TSP-hork/R.I.G.E.L_Robotic_Manipulator/cad/manufacturing/stl/RIGEL/Reducers/20to1/final_20_1_fastdisk_1.1.stl

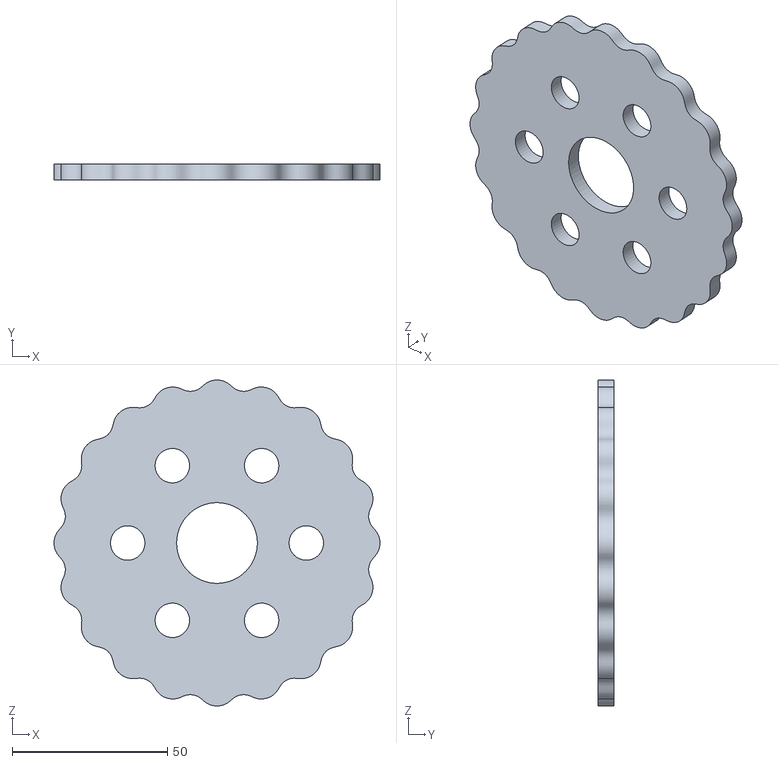
[picture p15: CAD file, 2026-10-07]
cad/manufacturing/stl/RIGEL/Reducers/20to1/final_20_1_fastdisk_1.1.stl
105.0 x 5.00 x 105.0
