TSP-hork/R.I.G.E.L_Robotic_Manipulator/cad/manufacturing/stl/RIGEL/Reducers/Adapter/adapter_V1.stl

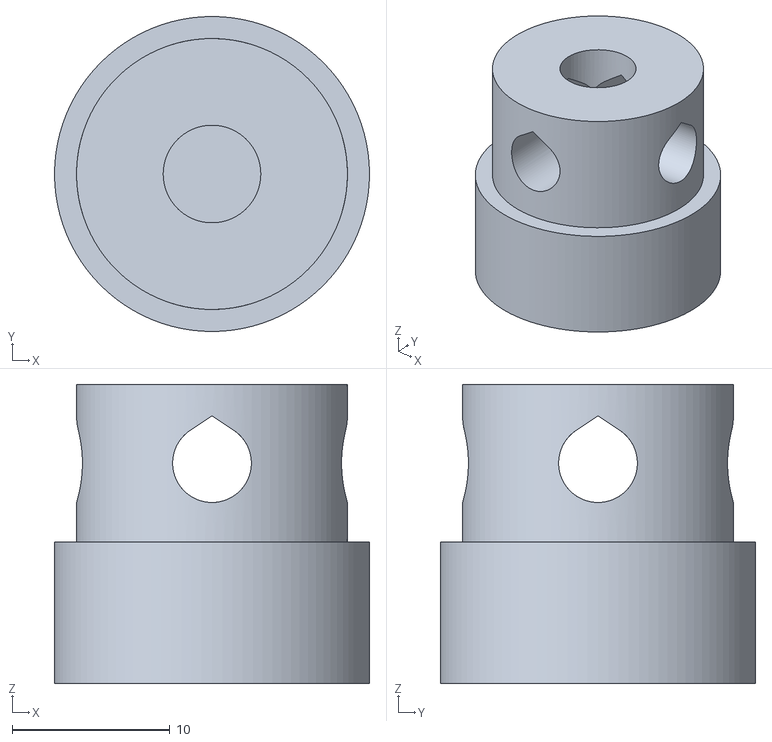
[picture p16: CAD file, 2026-10-07]
cad/manufacturing/stl/RIGEL/Reducers/Adapter/adapter_V1.stl
20.0 x 20.0 x 19.0
