TSP-hork/R.I.G.E.L_Robotic_Manipulator/cad/manufacturing/stl/RIGEL/Shoulder_Clevis_Mount/wheel_60.stl

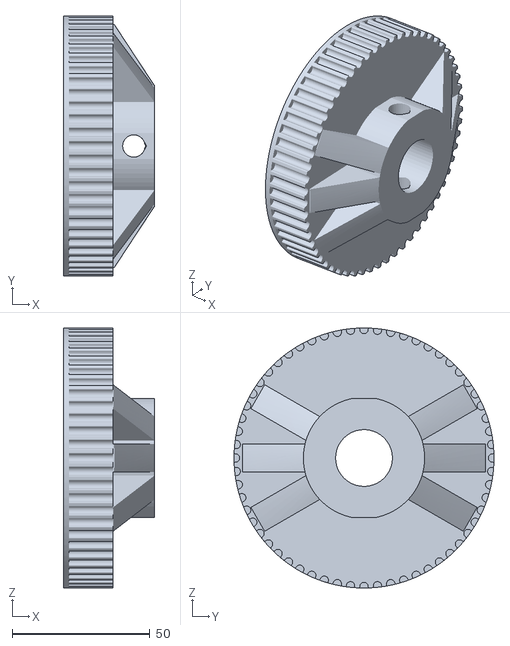
[picture p17: CAD file, 2026-10-07]
cad/manufacturing/stl/RIGEL/Shoulder_Clevis_Mount/wheel_60.stl
33.0 x 94.3 x 94.3
