TSP-hork/R.I.G.E.L_Robotic_Manipulator/cad/manufacturing/stl/RIGEL/Shoulder_module_short/Left_ear.stl

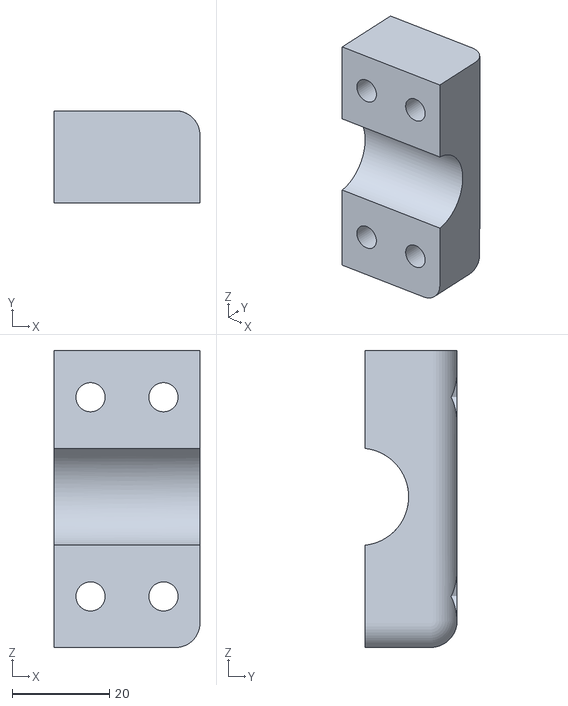
[picture p18: CAD file, 2026-10-07]
cad/manufacturing/stl/RIGEL/Shoulder_module_short/Left_ear.stl
30.0 x 19.0 x 61.1
