TSP-hork/R.I.G.E.L_Robotic_Manipulator/cad/manufacturing/stl/RIGEL/Actuator_module/Actuator_module_part.stl

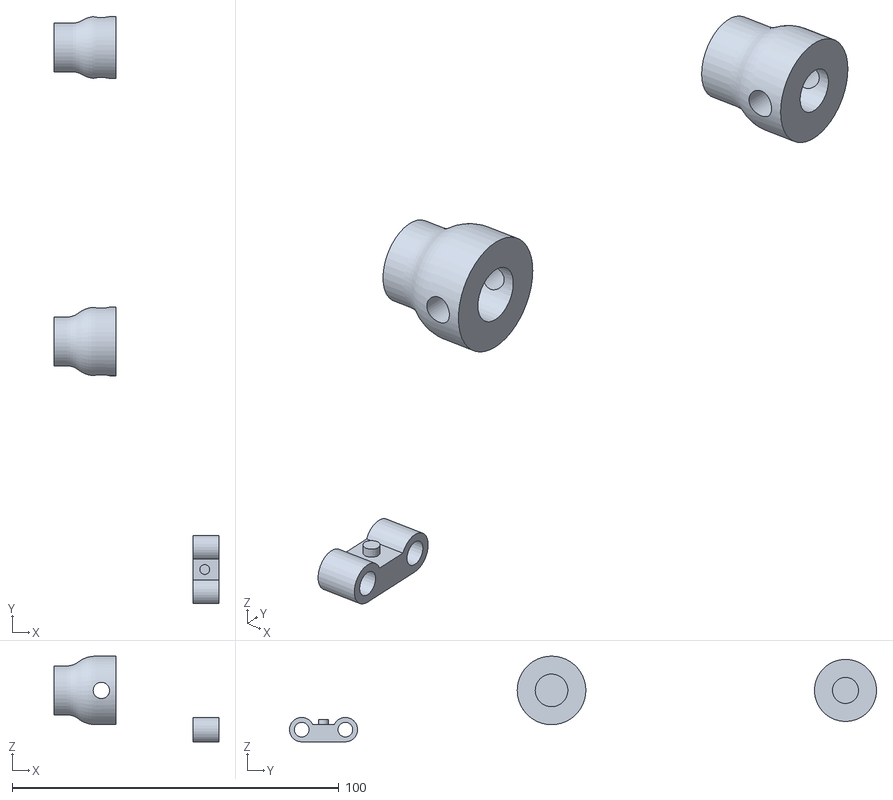
[picture p19: CAD file, 2026-10-07]
cad/manufacturing/stl/RIGEL/Actuator_module/Actuator_module_part.stl
50.5 x 179.7 x 26.3
