TSP-hork/R.I.G.E.L_Robotic_Manipulator/cad/manufacturing/stl/RIGEL/Reducers/Adapter/adapter_rotary_reducer_V1.1.stl

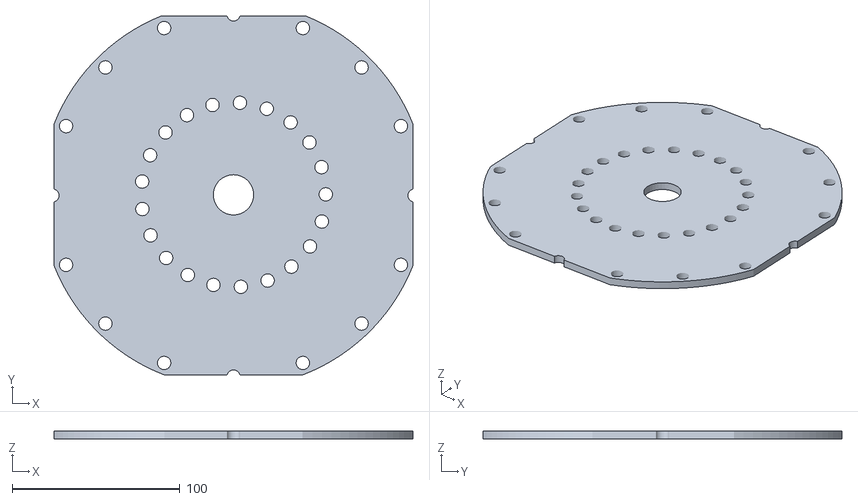
[picture p20: CAD file, 2026-10-07]
cad/manufacturing/stl/RIGEL/Reducers/Adapter/adapter_rotary_reducer_V1.1.stl
214.0 x 214.0 x 5.00
