TSP-hork/R.I.G.E.L_Robotic_Manipulator/cad/manufacturing/stl/RIGEL/Shoulder_Clevis_Mount/Shoulder_Clevis_Mount_V1.3_part.stl

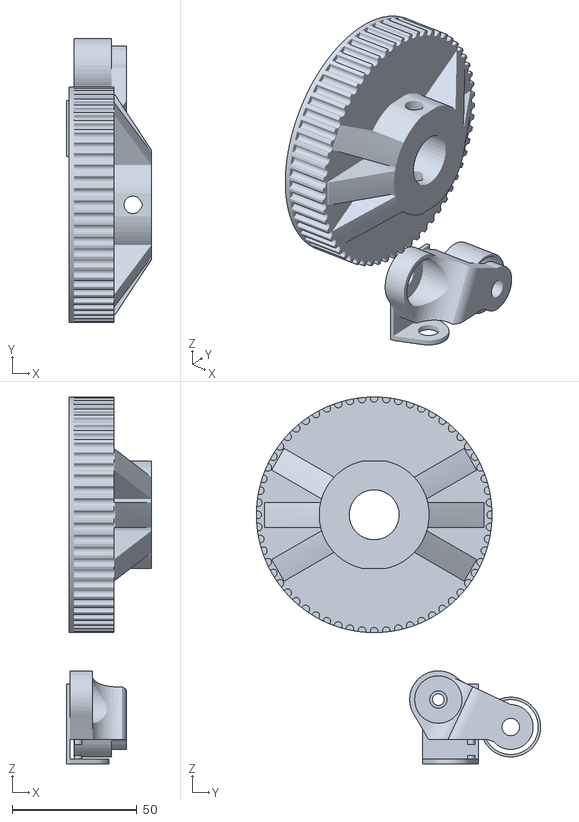
[picture p21: CAD file, 2026-10-07]
cad/manufacturing/stl/RIGEL/Shoulder_Clevis_Mount/Shoulder_Clevis_Mount_V1.3_part.stl
34.0 x 113.8 x 147.0
