TSP-hork/R.I.G.E.L_Robotic_Manipulator/cad/manufacturing/stl/RIGEL/Shoulder_module_long/Body_of_1shoulder_module_V1.2_down.stl

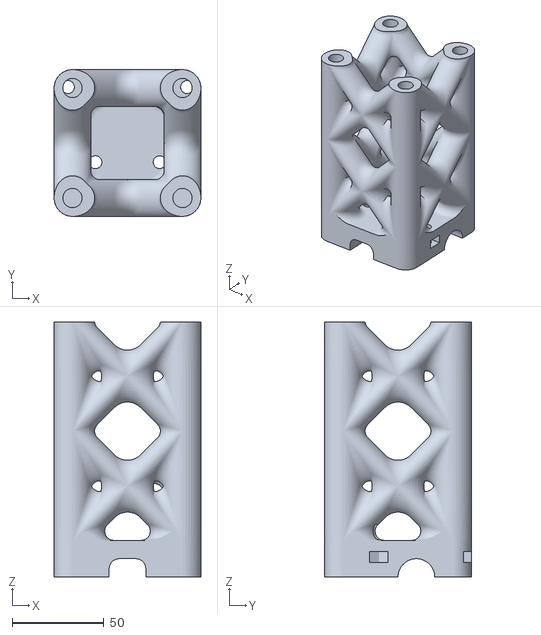
[picture p22: CAD file, 2026-10-07]
cad/manufacturing/stl/RIGEL/Shoulder_module_long/Body_of_1shoulder_module_V1.2_down.stl
80.0 x 80.0 x 139.0
