TSP-hork/R.I.G.E.L_Robotic_Manipulator/cad/manufacturing/stl/RIGEL/Shoulder_module_short/Body_of_2shoulder_module.stl

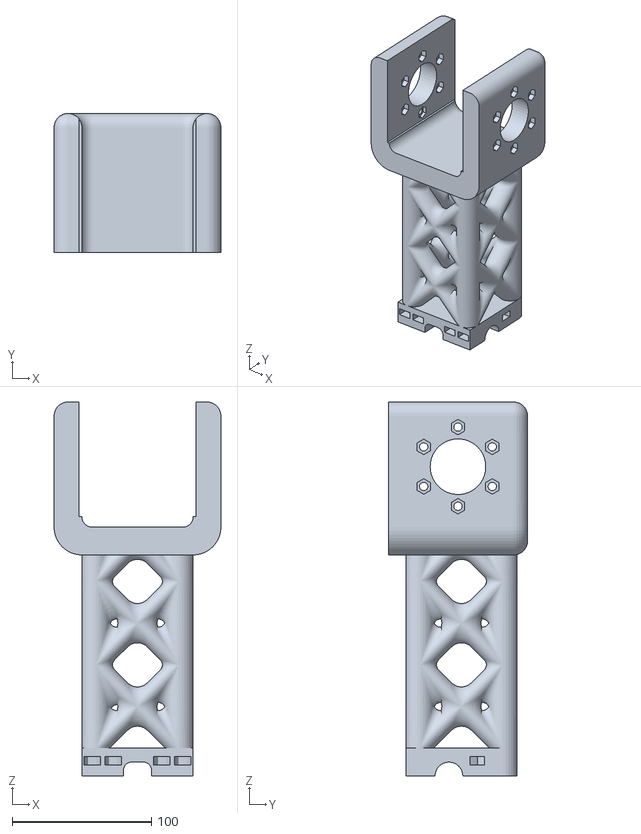
[picture p23: CAD file, 2026-10-07]
cad/manufacturing/stl/RIGEL/Shoulder_module_short/Body_of_2shoulder_module.stl
120.0 x 100.0 x 269.0
