TSP-hork/R.I.G.E.L_Robotic_Manipulator/cad/manufacturing/stl/RIGEL/Reducers/Adapter/adapter_V1.1_8mm.stl

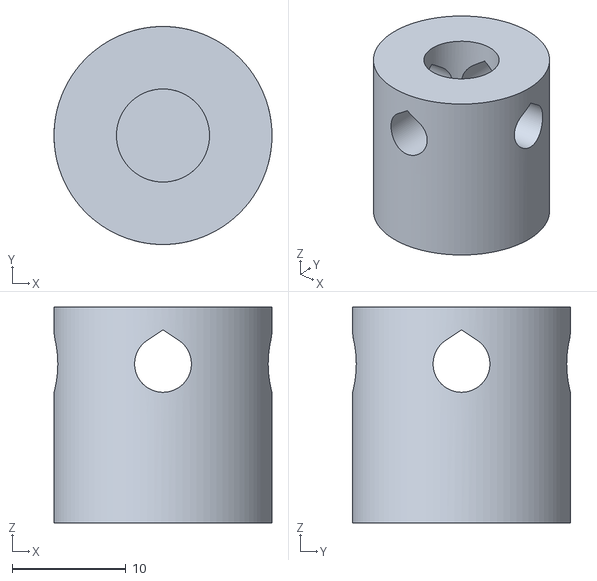
[picture p24: CAD file, 2026-10-07]
cad/manufacturing/stl/RIGEL/Reducers/Adapter/adapter_V1.1_8mm.stl
19.2 x 19.2 x 19.0
