TSP-hork/R.I.G.E.L_Robotic_Manipulator/cad/manufacturing/stl/RIGEL/Shoulder_Clevis_Mount/stator_holder.stl

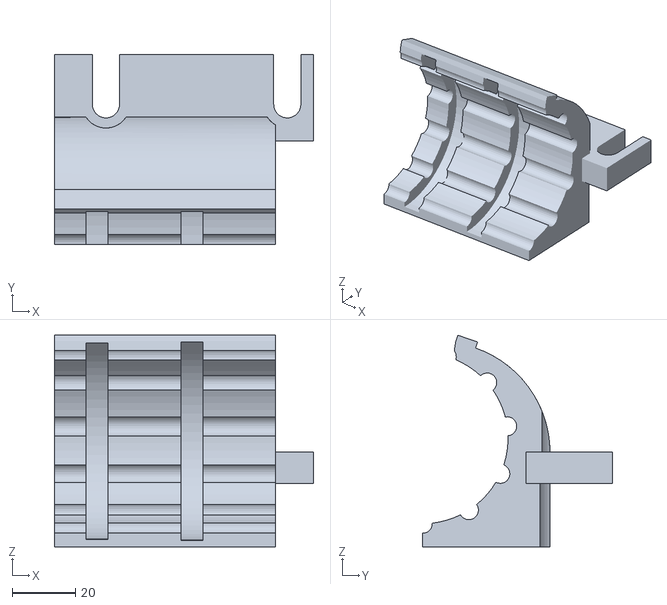
[picture p25: CAD file, 2026-10-07]
cad/manufacturing/stl/RIGEL/Shoulder_Clevis_Mount/stator_holder.stl
82.0 x 60.0 x 67.0
