TSP-hork/R.I.G.E.L_Robotic_Manipulator/cad/manufacturing/stl/RIGEL/Shoulder_module_long/Body_of_1shoulder_module_V1.1.stl

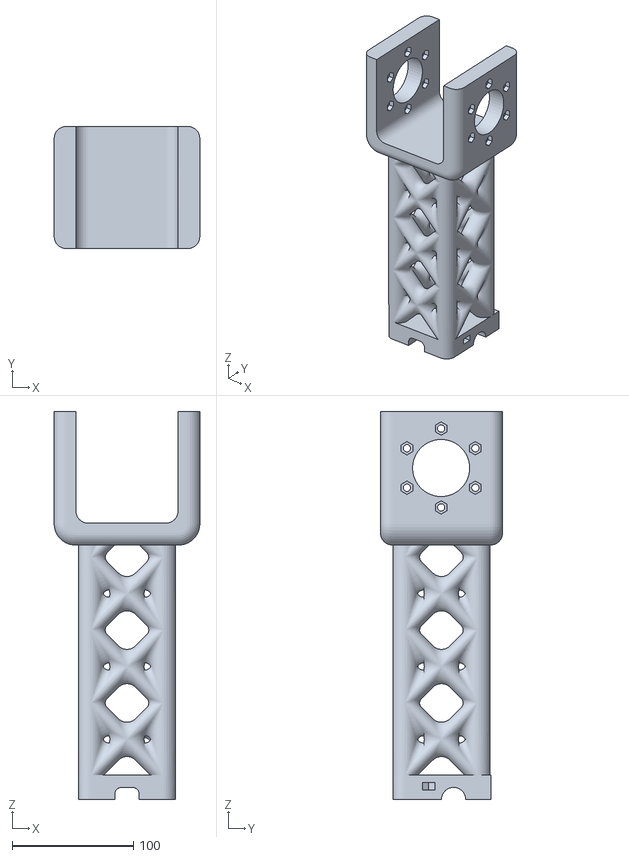
[picture p26: CAD file, 2026-10-07]
cad/manufacturing/stl/RIGEL/Shoulder_module_long/Body_of_1shoulder_module_V1.1.stl
120.0 x 100.6 x 319.5
