TSP-hork/R.I.G.E.L_Robotic_Manipulator/cad/manufacturing/stl/RIGEL/Reducers/Adapter/adapter_rotary_reducer_.stl

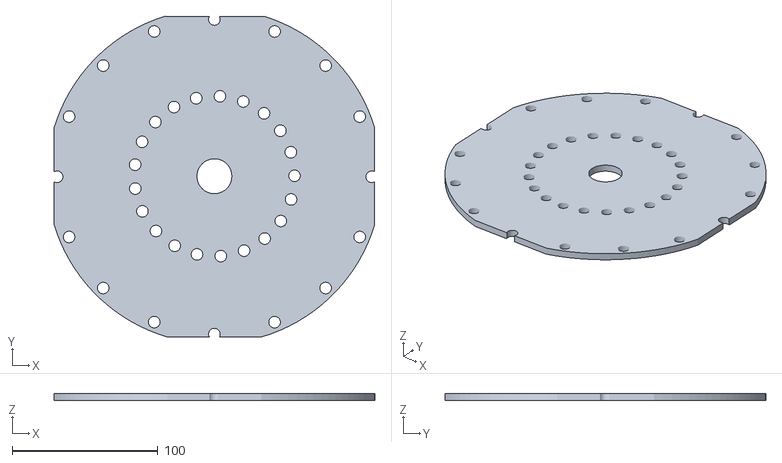
[picture p27: CAD file, 2026-10-07]
cad/manufacturing/stl/RIGEL/Reducers/Adapter/adapter_rotary_reducer_.stl
220.1 x 220.4 x 5.00
